muething/IONOS-SIM/IONOS_SIM_Channel_Simulator/IONOS SIM_Documentation/Lafleur_DC-45PMBYT_ASS'Y v5 boxonly.png

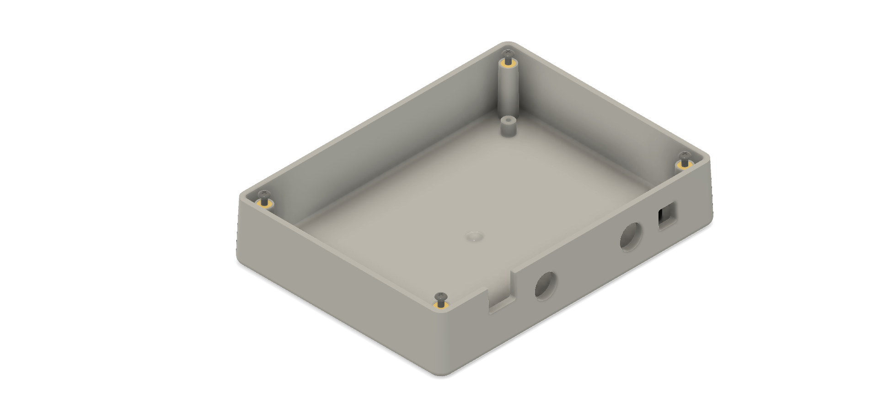
IONOS_SIM_Channel_Simulator/IONOS SIM_Documentation/Lafleur_DC-45PMBYT_ASS'Y v5 boxonly.png
